dudasdavid/MaM2019/Mechanics/STL/mainframe/pcb_holder.STL

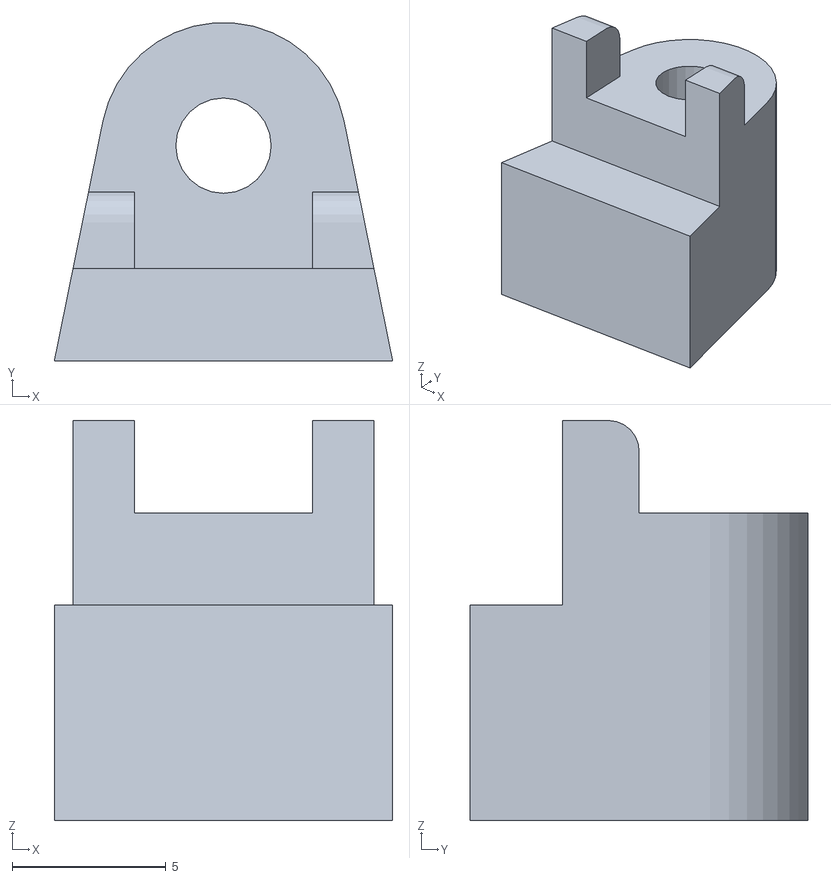
[picture p17: CAD file, 2020-09-13]
Mechanics/STL/mainframe/pcb_holder.STL
11.0 x 11.0 x 13.0
