dudasdavid/MaM2019/Mechanics/STL/tower/rib.STL

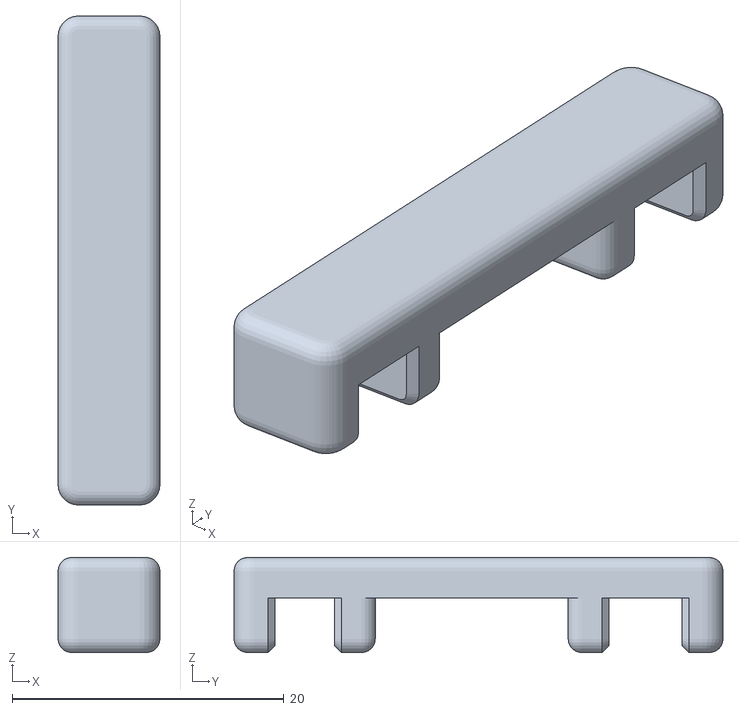
[picture p18: CAD file, 2020-09-15]
Mechanics/STL/tower/rib.STL
7.50 x 36.0 x 7.00
