dudasdavid/MaM2019/Mechanics/Gear design/spur_gear.dxf

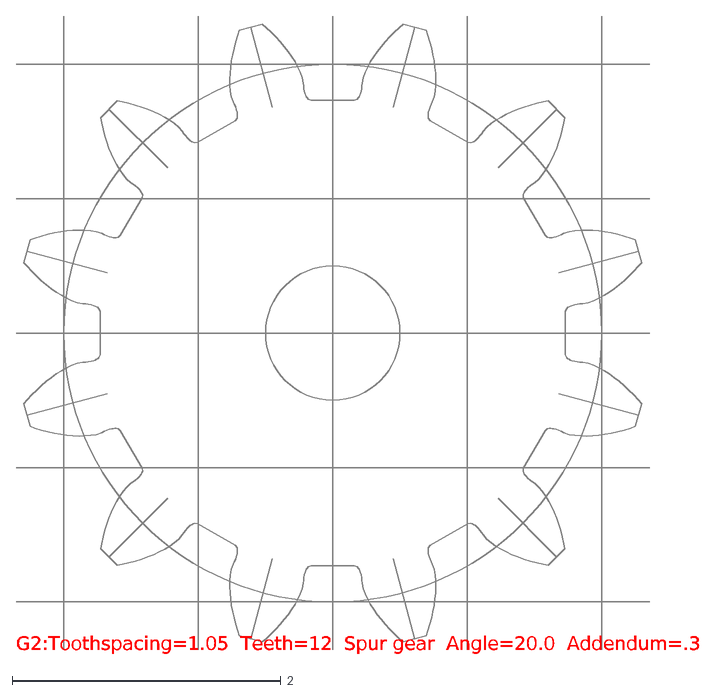
[picture p19: CAD file, 2019-07-08]
Mechanics/Gear design/spur_gear.dxf
G2:Toothspacing=1.05 Teeth=12 Spur gear Angle=20.0 Addendum=.3
