dudasdavid/MaM2019/Mechanics/Solidworks/SG90/microservoArm.SLDPRT

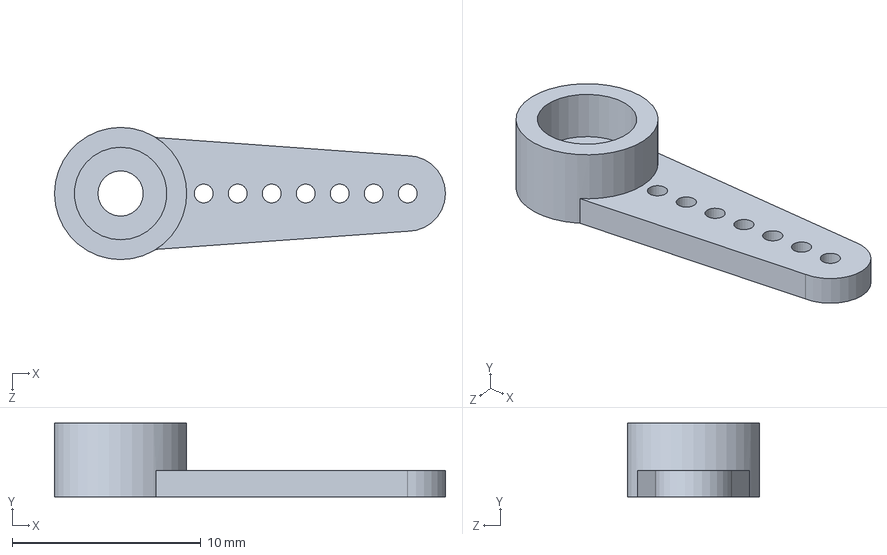
[picture p20: CAD file, 2020-09-13]
Mechanics/Solidworks/SG90/microservoArm.SLDPRT
20.7 x 3.90 x 7.00 mm
