dudasdavid/MaM2019/Mechanics/STL/camera/part1.STL

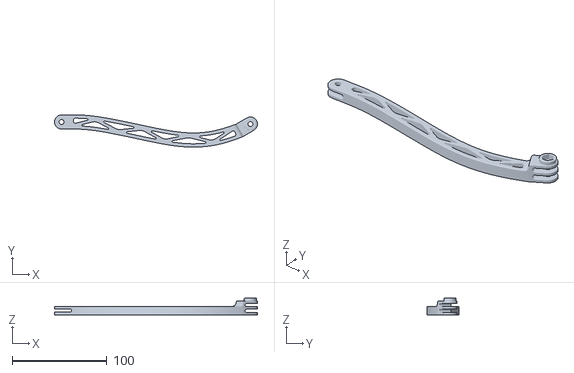
[picture p21: CAD file, 2020-09-19]
Mechanics/STL/camera/part1.STL
214.4 x 34.1 x 17.8
