dudasdavid/MaM2019/Mechanics/STL/ejector/cap.STL

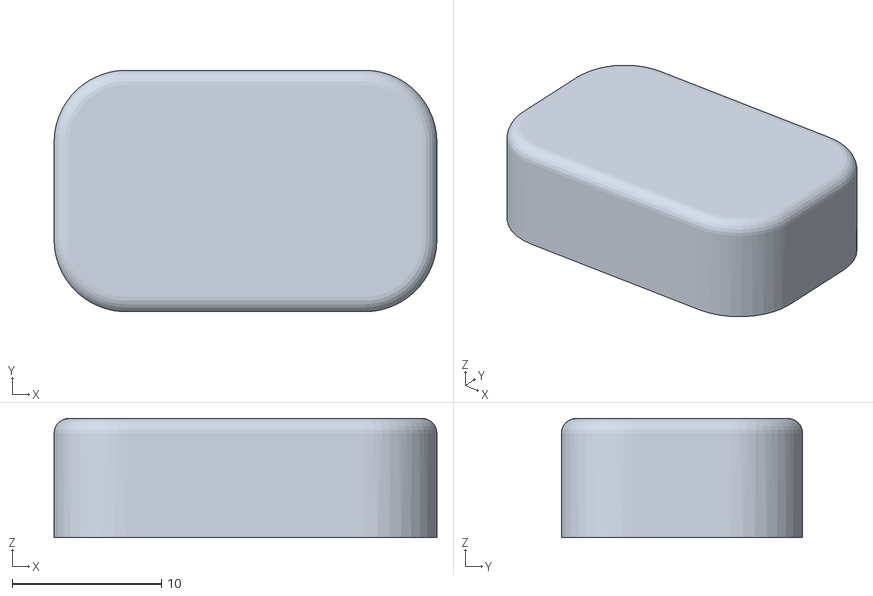
[picture p22: CAD file, 2020-09-15]
Mechanics/STL/ejector/cap.STL
25.7 x 16.2 x 8.00
