dudasdavid/MaM2019/Mechanics/STL/mainframe/side2_unmirrored.STL

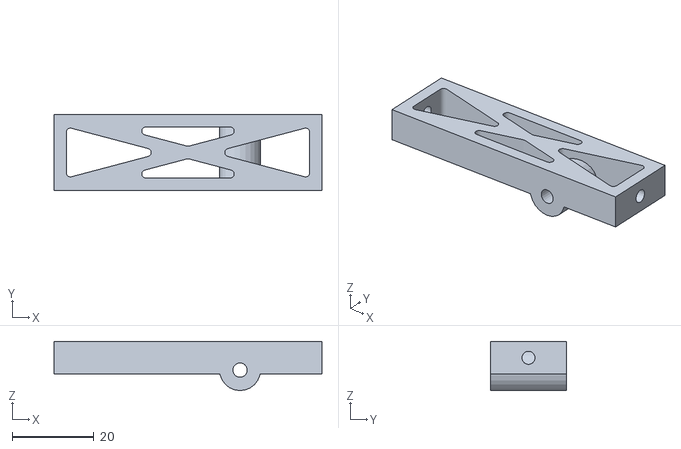
[picture p23: CAD file, 2020-09-13]
Mechanics/STL/mainframe/side2_unmirrored.STL
65.4 x 18.5 x 12.0
