dudasdavid/MaM2019/Mechanics/STL/tower/COLLECTOR2.STL

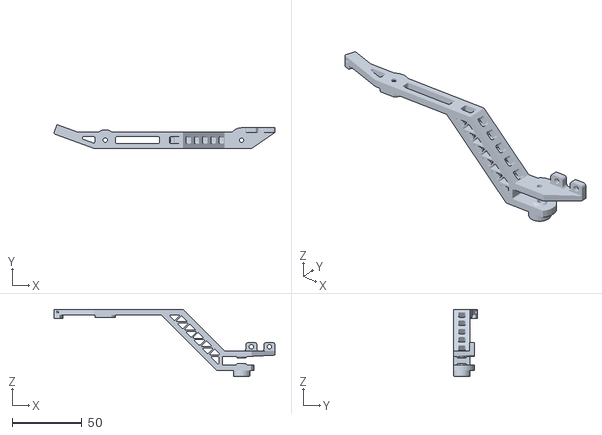
[picture p24: CAD file, 2020-09-13]
Mechanics/STL/tower/COLLECTOR2.STL
158.8 x 17.2 x 48.5
