dudasdavid/MaM2019/Mechanics/Gear design/gears_v1.dxf

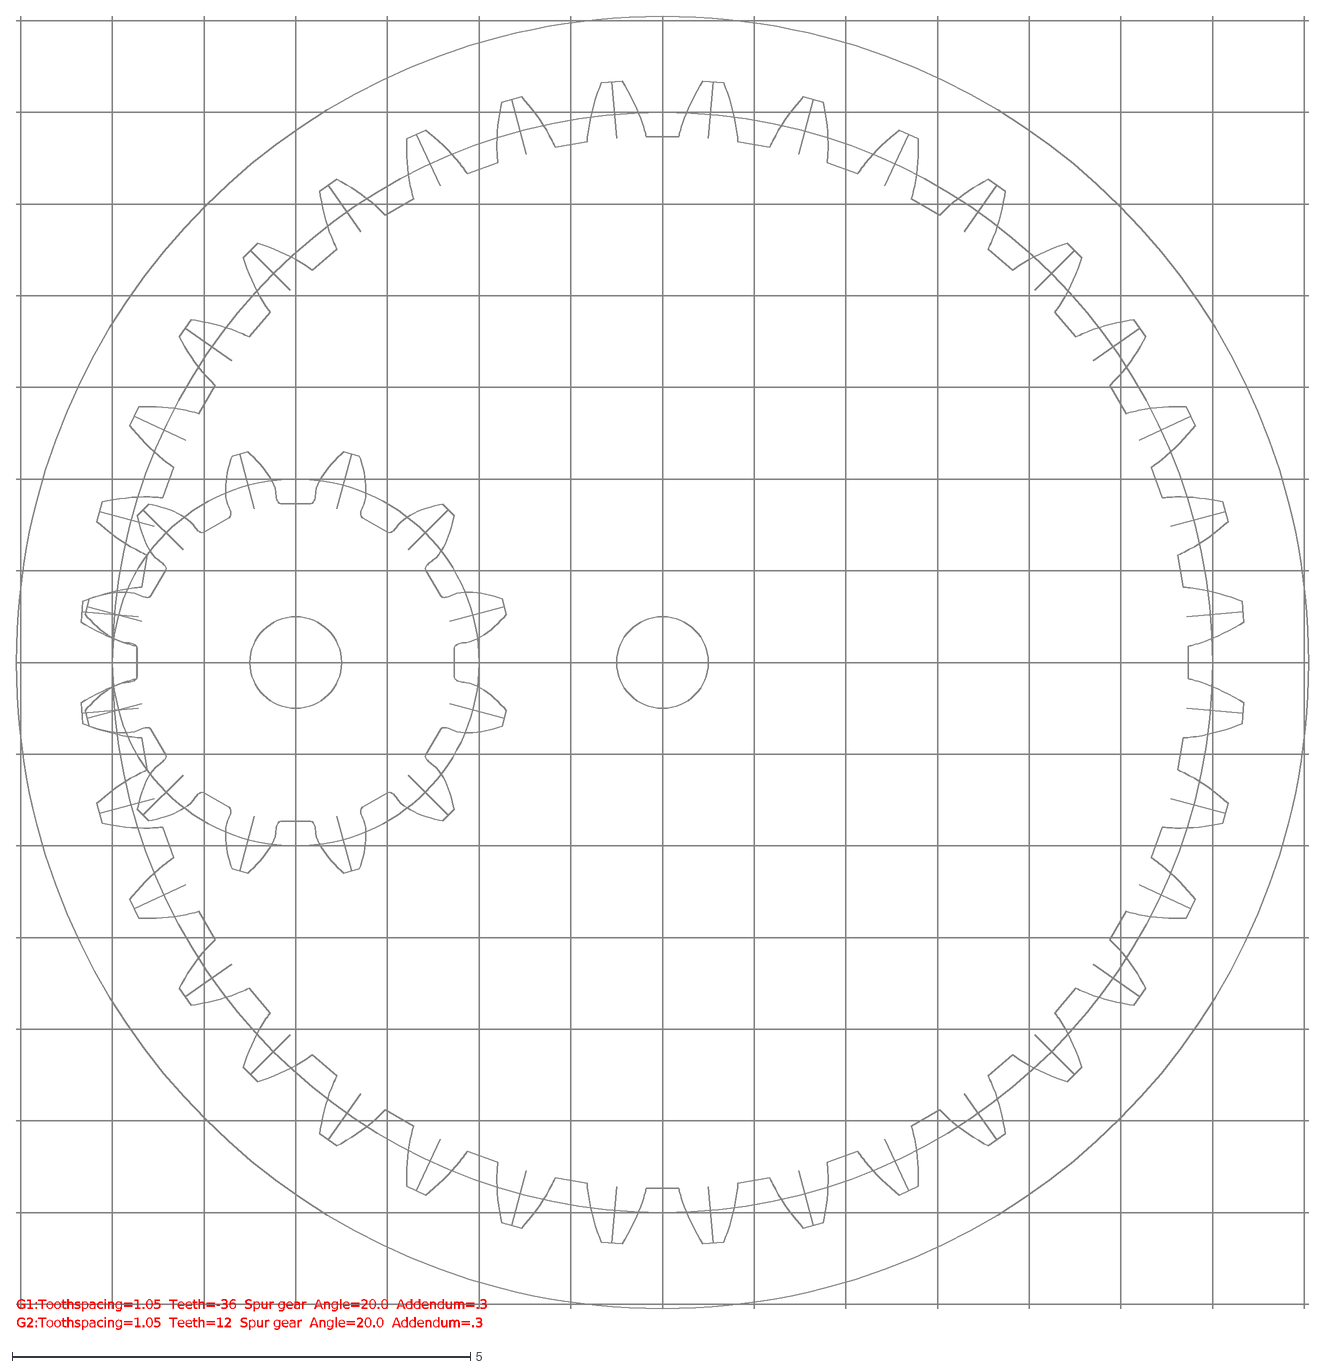
[picture p25: CAD file, 2019-07-08]
Mechanics/Gear design/gears_v1.dxf
G1:Toothspacing=1.05 Teeth=-36 Spur gear Angle=20.0 Addendum=.3
G2:Toothspacing=1.05 Teeth=12 Spur gear Angle=20.0 Addendum=.3
