dudasdavid/MaM2019/Mechanics/STL/camera/camera_frame.STL

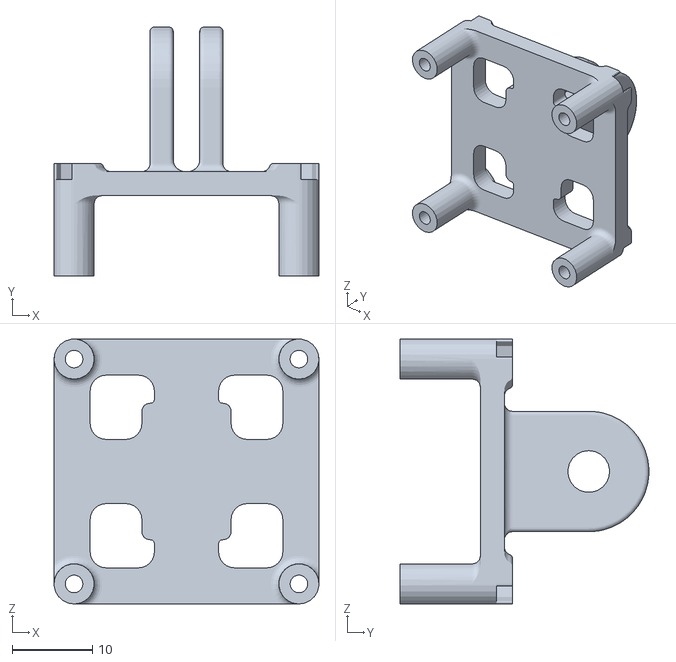
[picture p26: CAD file, 2020-09-19]
Mechanics/STL/camera/camera_frame.STL
33.0 x 31.0 x 33.0
