dudasdavid/MaM2019/Mechanics/STL/ejector/arm.STL

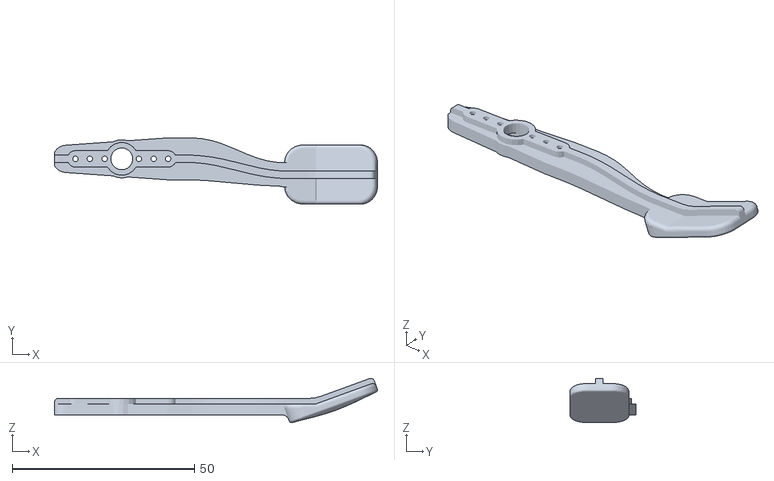
[picture p27: CAD file, 2020-09-15]
Mechanics/STL/ejector/arm.STL
88.5 x 18.2 x 12.2
