dudasdavid/MaM2019/Mechanics/STL/mainframe/base_1.STL

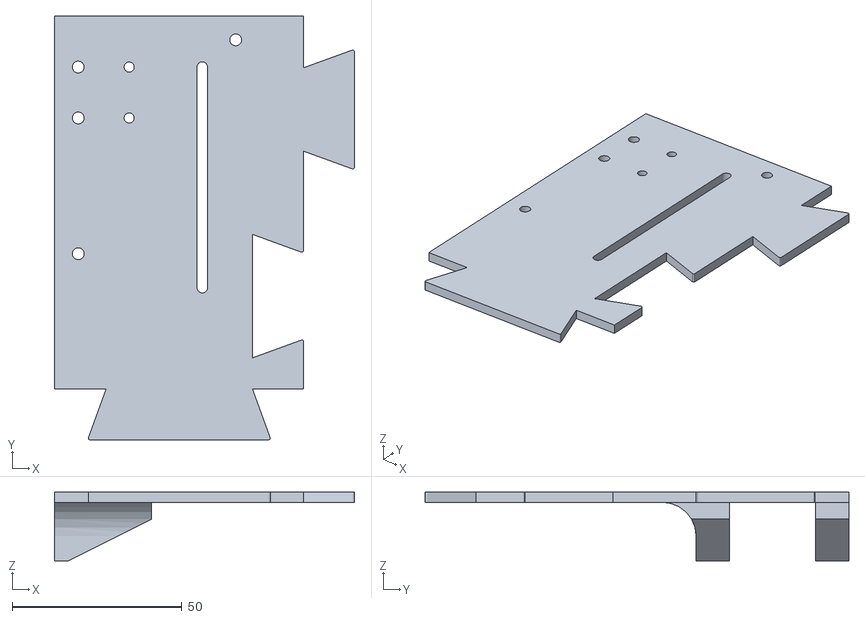
[picture p28: CAD file, 2020-09-13]
Mechanics/STL/mainframe/base_1.STL
88.4 x 124.8 x 20.3
