dudasdavid/MaM2019/Mechanics/STL/tower/COLLECTOR3.STL

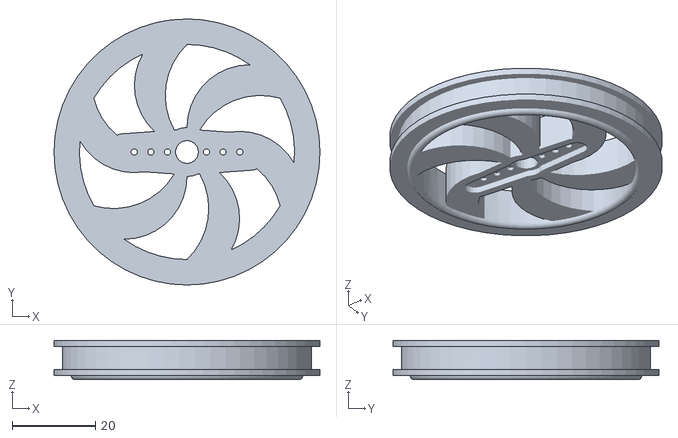
[picture p29: CAD file, 2020-09-13]
Mechanics/STL/tower/COLLECTOR3.STL
64.0 x 64.0 x 9.50
