dudasdavid/MaM2019/Mechanics/STL/camera/part2.STL

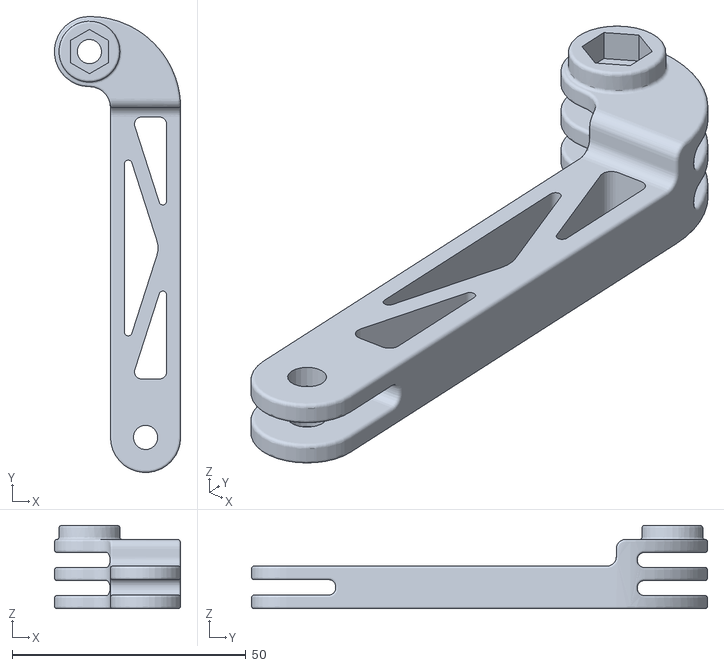
[picture p30: CAD file, 2020-09-19]
Mechanics/STL/camera/part2.STL
27.0 x 97.5 x 17.8
