dudasdavid/MaM2019/Mechanics/STL/ejector/bag.STL

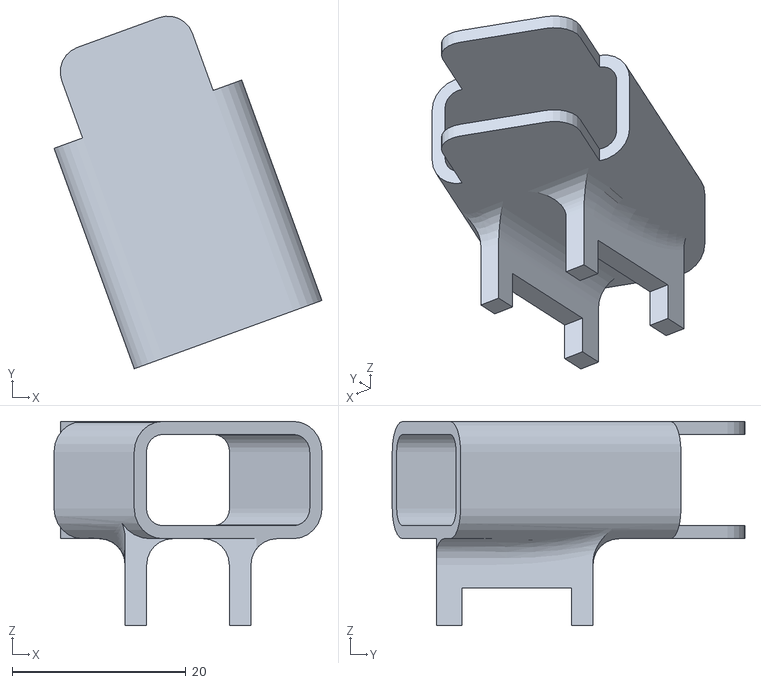
[picture p31: CAD file, 2020-09-15]
Mechanics/STL/ejector/bag.STL
30.8 x 40.6 x 23.5
