dudasdavid/MaM2019/Mechanics/STL/mainframe/side1_unmirrored.STL

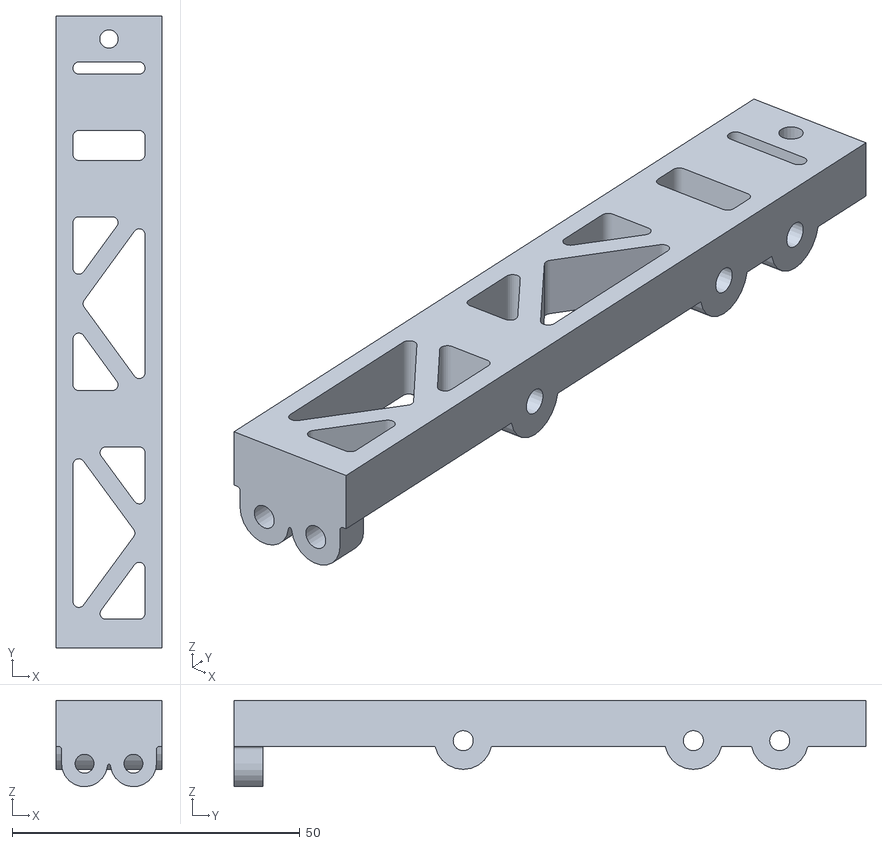
[picture p32: CAD file, 2020-09-13]
Mechanics/STL/mainframe/side1_unmirrored.STL
18.5 x 109.8 x 15.0
