dudasdavid/MaM2019/Mechanics/STL/tower/right.STL

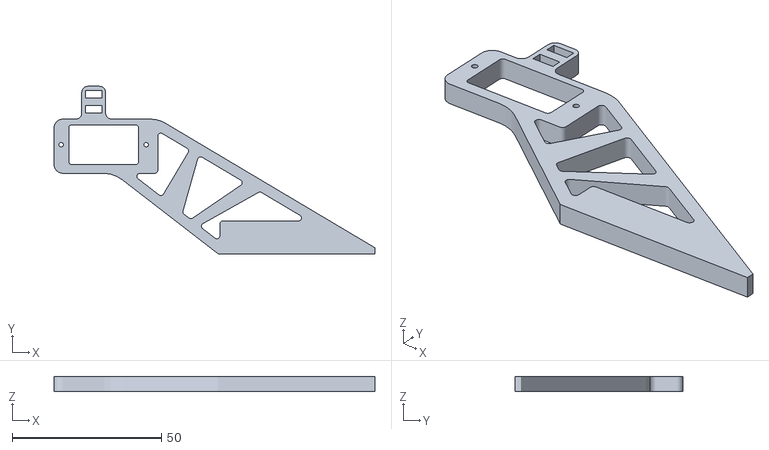
[picture p33: CAD file, 2020-09-13]
Mechanics/STL/tower/right.STL
107.6 x 56.1 x 5.00
