dudasdavid/MaM2019/Mechanics/STL/ejector/ball_remover.STL

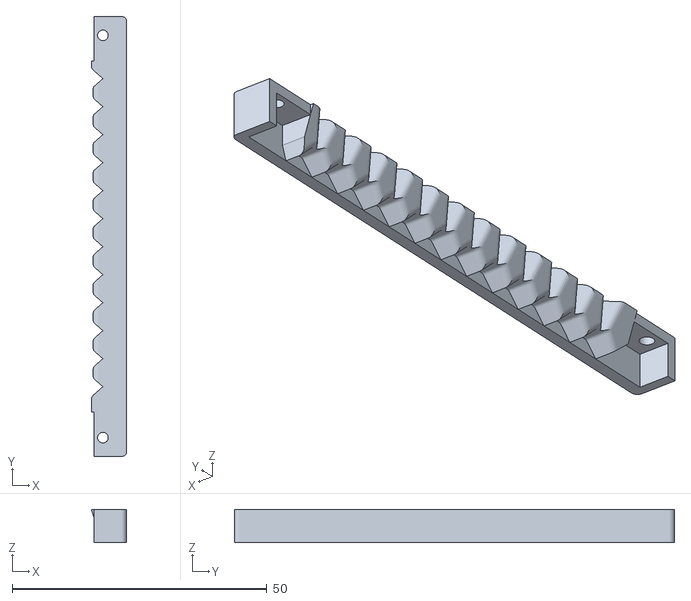
[picture p34: CAD file, 2020-09-15]
Mechanics/STL/ejector/ball_remover.STL
6.97 x 86.4 x 6.50
