dudasdavid/MaM2019/Mechanics/STL/mainframe/base_2.STL

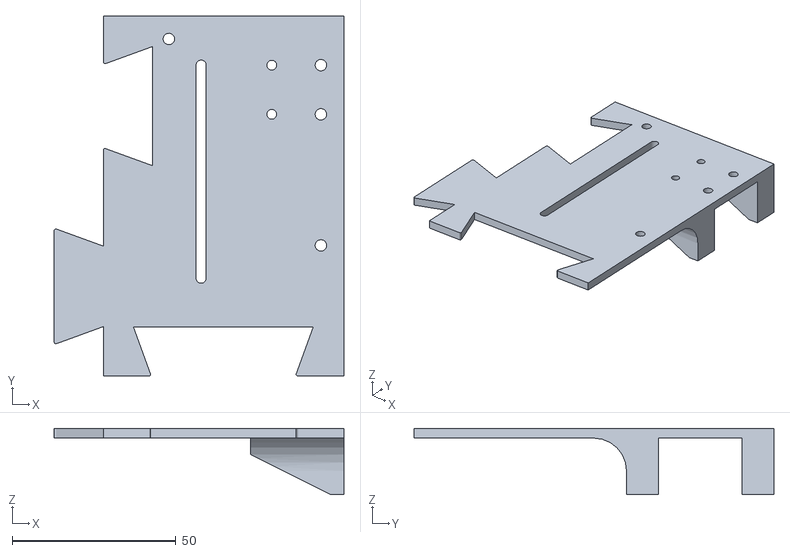
[picture p35: CAD file, 2020-09-13]
Mechanics/STL/mainframe/base_2.STL
88.4 x 109.8 x 20.3
