dudasdavid/MaM2019/Mechanics/STL/tower/COLLECTOR6.STL

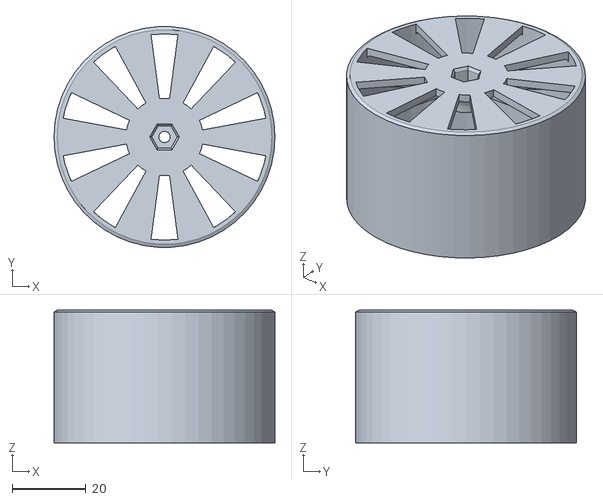
[picture p36: CAD file, 2020-09-13]
Mechanics/STL/tower/COLLECTOR6.STL
60.0 x 59.9 x 36.0
