dudasdavid/MaM2019/Mechanics/STL/tower/balance2.STL

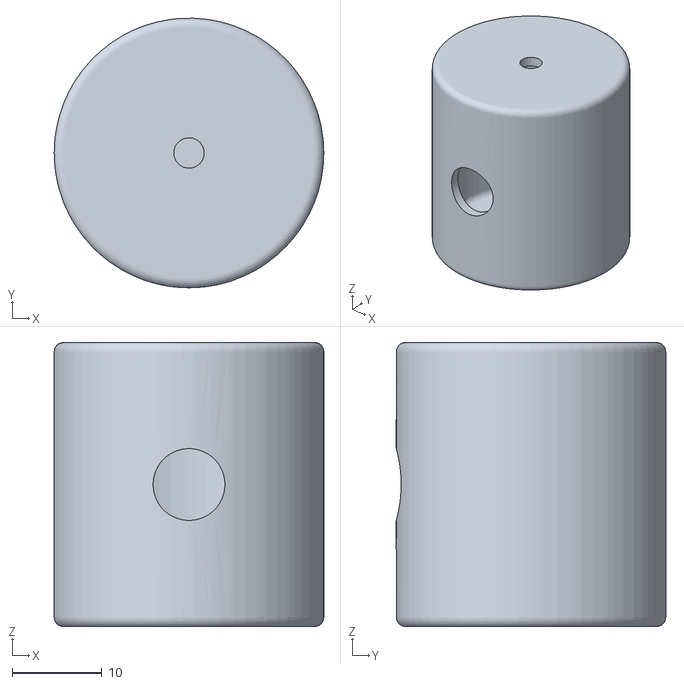
[picture p37: CAD file, 2020-09-13]
Mechanics/STL/tower/balance2.STL
30.0 x 30.0 x 31.6
