dudasdavid/MaM2019/Mechanics/STL/tower/balance1.STL

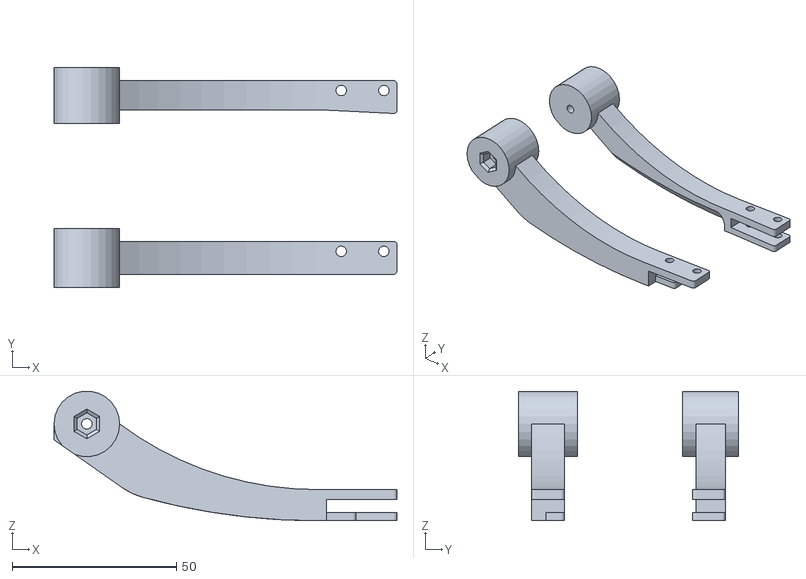
[picture p38: CAD file, 2020-09-13]
Mechanics/STL/tower/balance1.STL
104.5 x 67.0 x 39.4
