dudasdavid/MaM2019/Mechanics/STL/tower/COLLECTOR4.STL

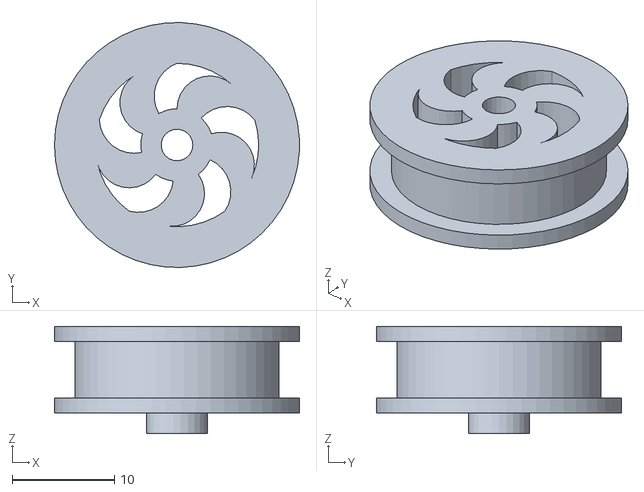
[picture p39: CAD file, 2020-09-13]
Mechanics/STL/tower/COLLECTOR4.STL
24.0 x 24.0 x 10.5
