dudasdavid/MaM2019/Mechanics/Solidworks/RingGear_corrected_diameter.SLDPRT

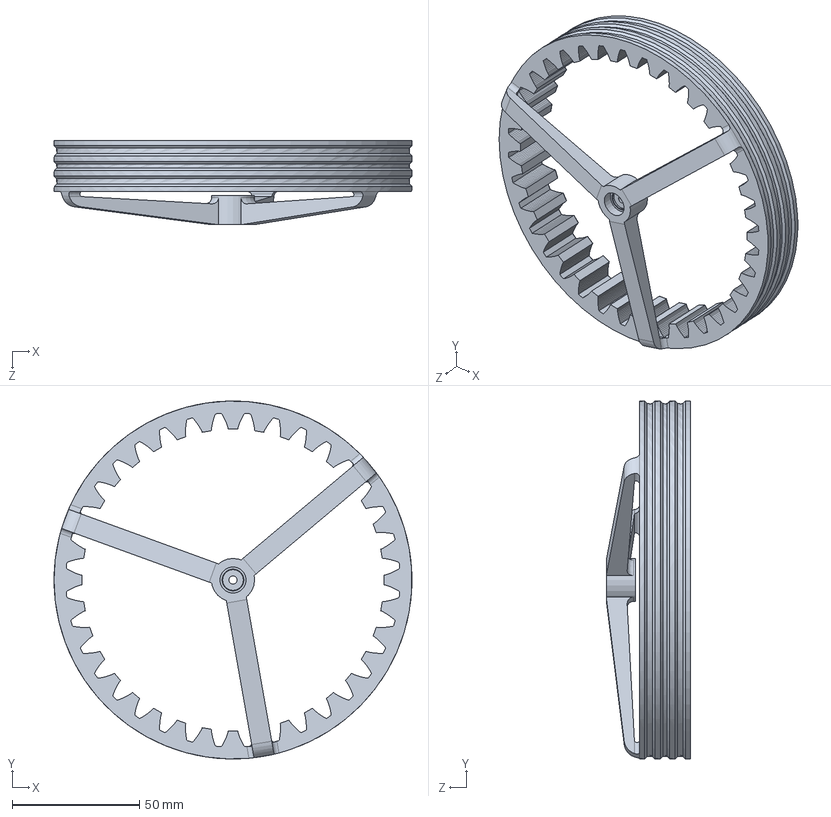
[picture p40: CAD file, 2020-09-13]
Mechanics/Solidworks/RingGear_corrected_diameter.SLDPRT
140.9 x 140.9 x 33.0 mm
