dudasdavid/MaM2019/Mechanics/STL/tower/middle.STL

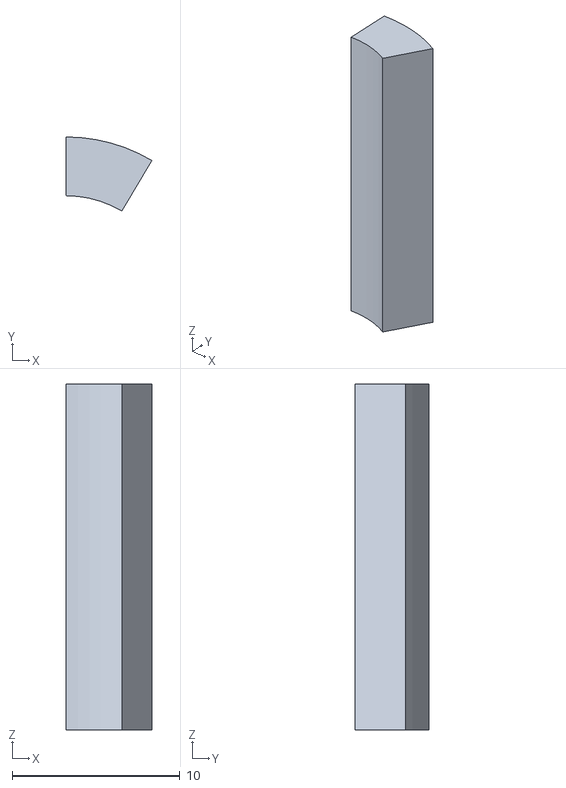
[picture p41: CAD file, 2020-09-13]
Mechanics/STL/tower/middle.STL
5.11 x 4.41 x 20.6
