dudasdavid/MaM2019/Mechanics/Solidworks/RubberTire shrinked.SLDPRT

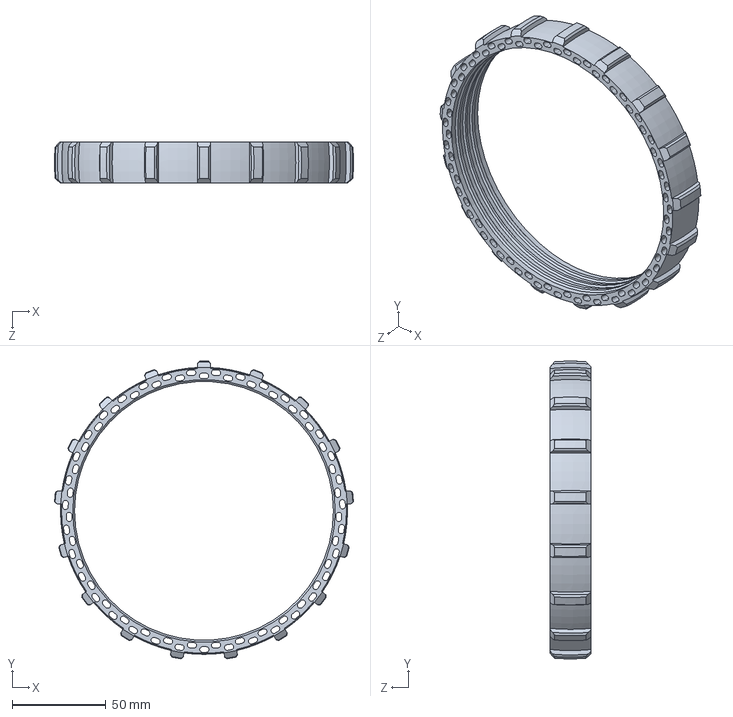
[picture p42: CAD file, 2020-09-13]
Mechanics/Solidworks/RubberTire shrinked.SLDPRT
159.1 x 158.5 x 22.0 mm
