dudasdavid/MaM2019/Mechanics/STL/tower/COLLECTOR1.STL

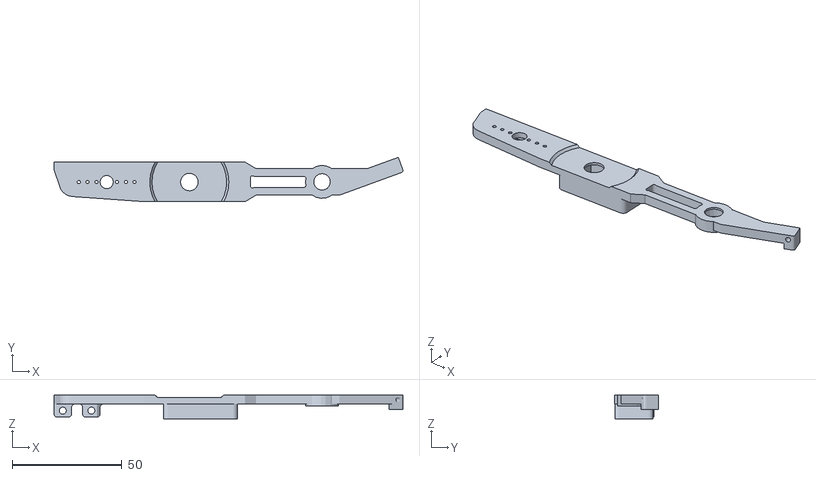
[picture p43: CAD file, 2020-09-13]
Mechanics/STL/tower/COLLECTOR1.STL
158.8 x 20.2 x 10.7
