dudasdavid/MaM2019/Mechanics/Solidworks/RingGear.SLDPRT

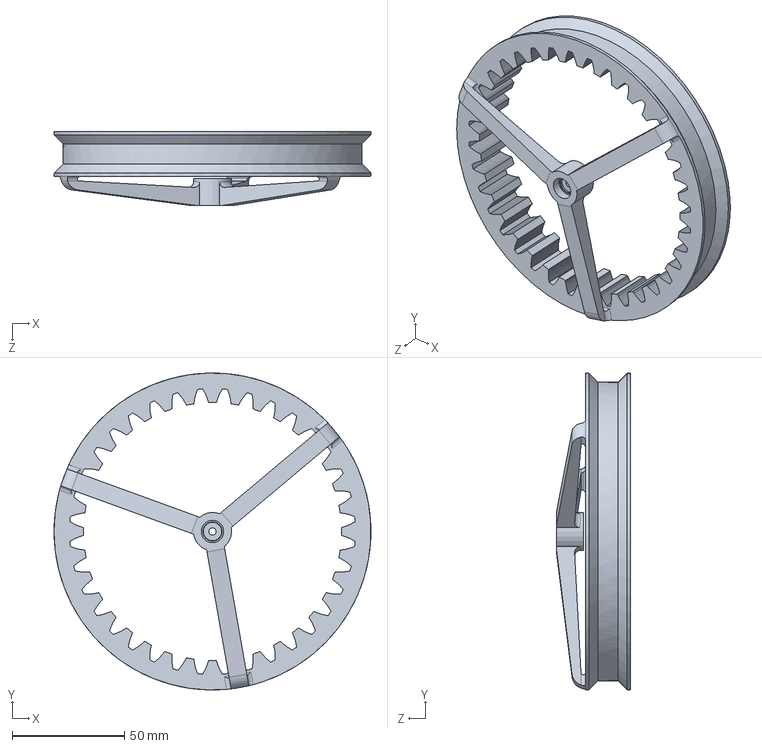
[picture p44: CAD file, 2020-09-13]
Mechanics/Solidworks/RingGear.SLDPRT
140.9 x 140.9 x 33.0 mm
