dudasdavid/MaM2019/Mechanics/STL/tower/base.STL

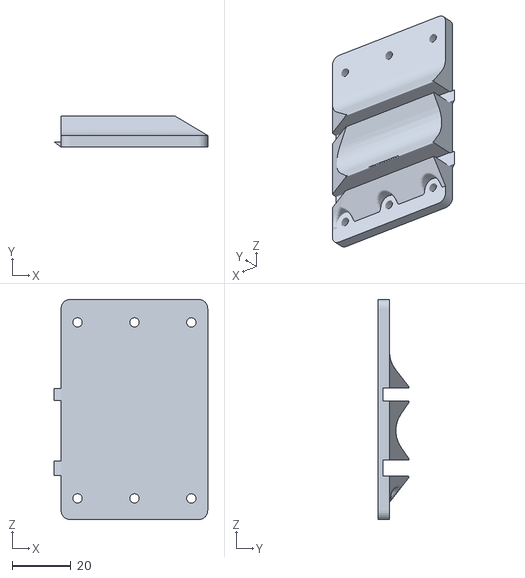
[picture p45: CAD file, 2020-09-13]
Mechanics/STL/tower/base.STL
52.3 x 10.7 x 75.0
