dudasdavid/MaM2019/Mechanics/Solidworks/Lbracket.sldprt

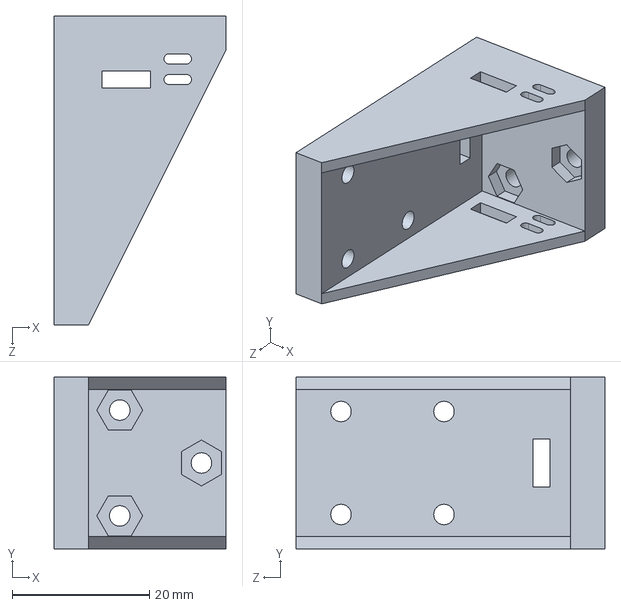
[picture p46: CAD file, 2020-09-13]
Mechanics/Solidworks/Lbracket.sldprt
25.0 x 25.0 x 45.0 mm
