dudasdavid/MaM2019/Mechanics/STL/tower/COLLECTOR5.STL

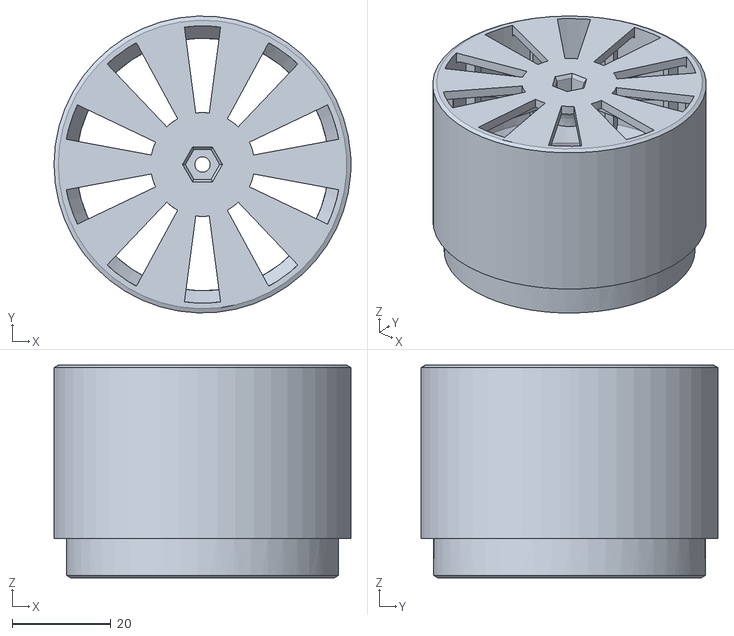
[picture p47: CAD file, 2020-09-13]
Mechanics/STL/tower/COLLECTOR5.STL
60.0 x 60.0 x 43.0
