dudasdavid/MaM2019/Mechanics/Solidworks/BasePlate.sldprt

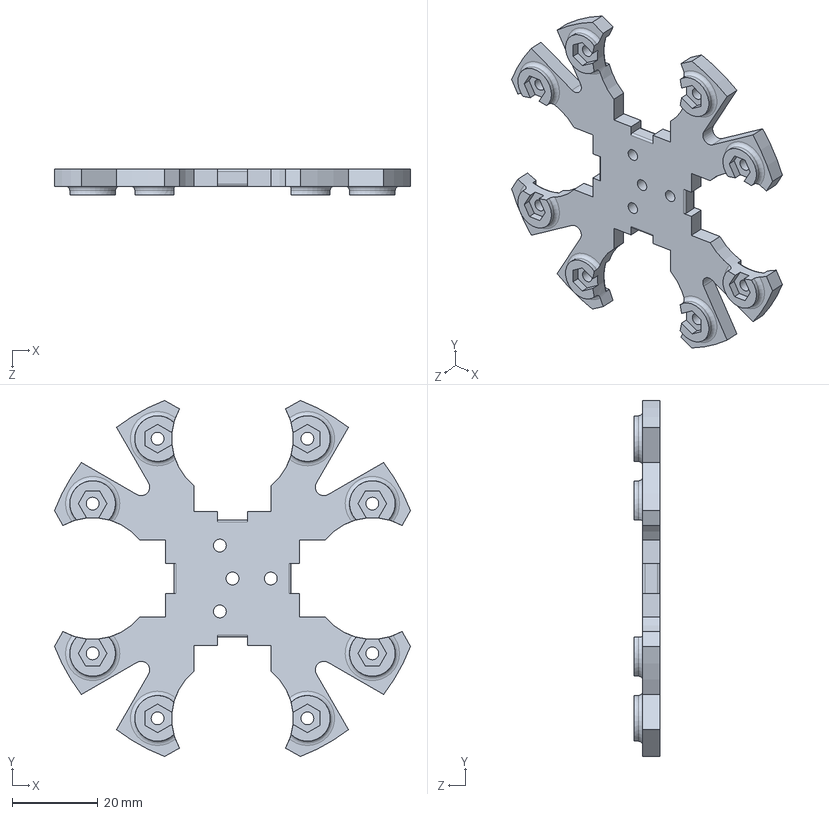
[picture p48: CAD file, 2020-09-13]
Mechanics/Solidworks/BasePlate.sldprt
83.2 x 83.2 x 6.00 mm
