dudasdavid/MaM2019/Mechanics/STL/tower/left.STL

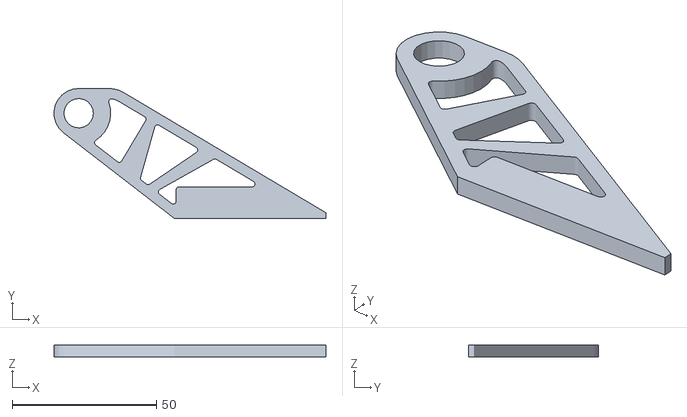
[picture p49: CAD file, 2020-09-13]
Mechanics/STL/tower/left.STL
94.4 x 45.1 x 4.00
