dudasdavid/MaM2019/Mechanics/Solidworks/SpurRibs_corrected.sldprt

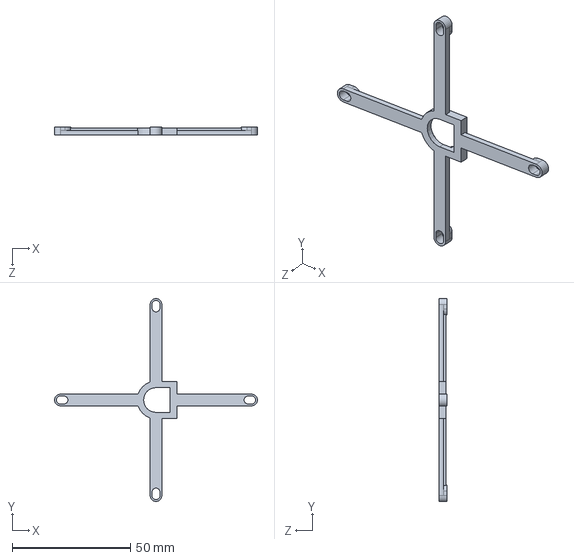
[picture p50: CAD file, 2020-09-13]
Mechanics/Solidworks/SpurRibs_corrected.sldprt
86.0 x 86.0 x 3.50 mm
