dudasdavid/MaM2019/Mechanics/Solidworks/SpurGear.SLDPRT

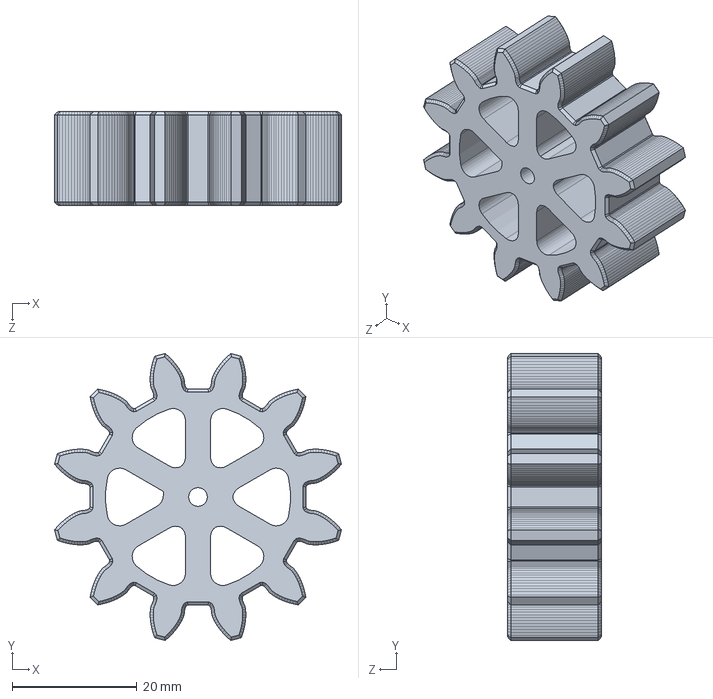
[picture p51: CAD file, 2020-09-13]
Mechanics/Solidworks/SpurGear.SLDPRT
45.9 x 45.9 x 15.0 mm
