dudasdavid/MaM2019/Mechanics/Solidworks/El2 - 28BYJ-48 - 5 VDC.SLDPRT

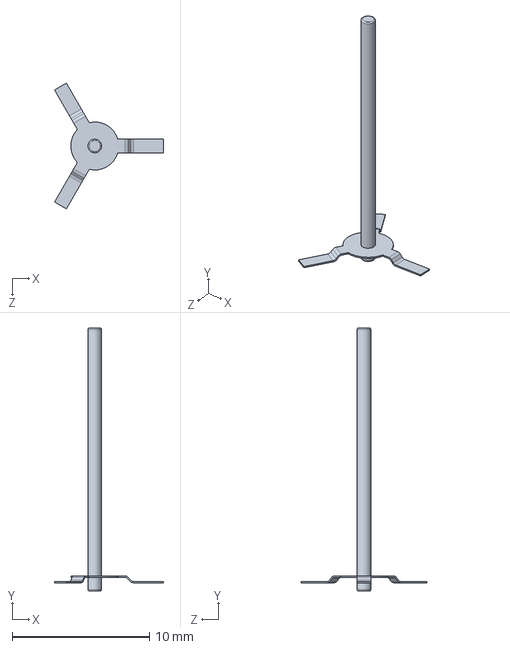
[picture p52: CAD file, 2020-09-13]
Mechanics/Solidworks/El2 - 28BYJ-48 - 5 VDC.SLDPRT
7.93 x 19.1 x 9.16 mm
