dudasdavid/MaM2019/Mechanics/Solidworks/El7 - 28BYJ-48 - 5 VDC.SLDPRT

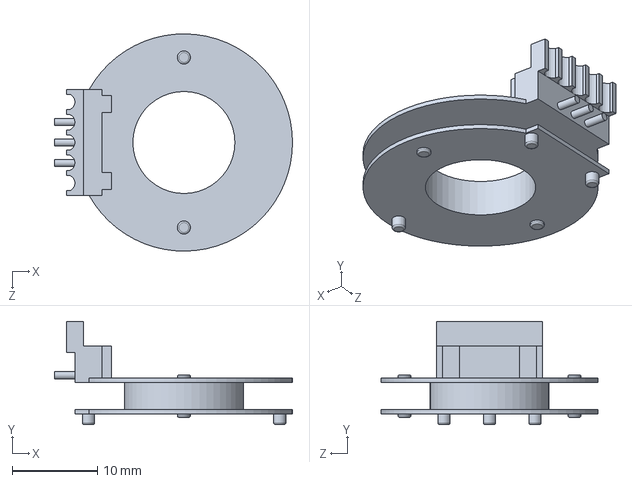
[picture p53: CAD file, 2020-09-13]
Mechanics/Solidworks/El7 - 28BYJ-48 - 5 VDC.SLDPRT
28.0 x 12.1 x 25.5 mm
