dudasdavid/MaM2019/Mechanics/Solidworks/El8 - 28BYJ-48 - 5 VDC.SLDPRT

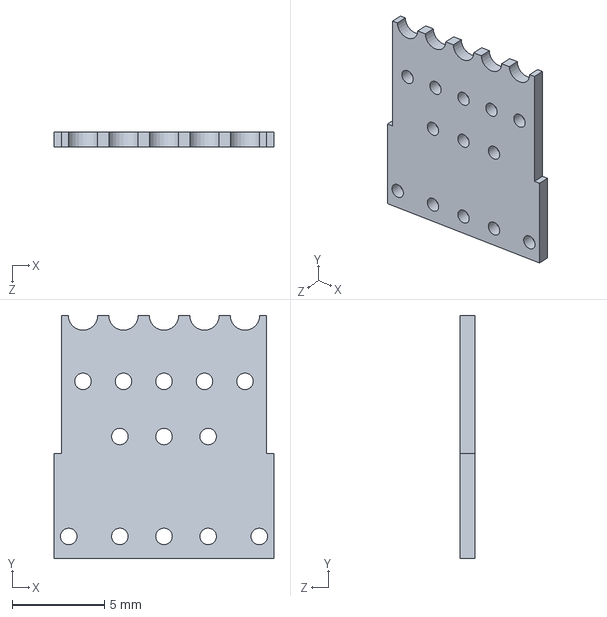
[picture p54: CAD file, 2020-09-13]
Mechanics/Solidworks/El8 - 28BYJ-48 - 5 VDC.SLDPRT
11.9 x 13.2 x 0.8 mm
