dudasdavid/MaM2019/Mechanics/Solidworks/El14 - 28BYJ-48 - 5 VDC.SLDPRT

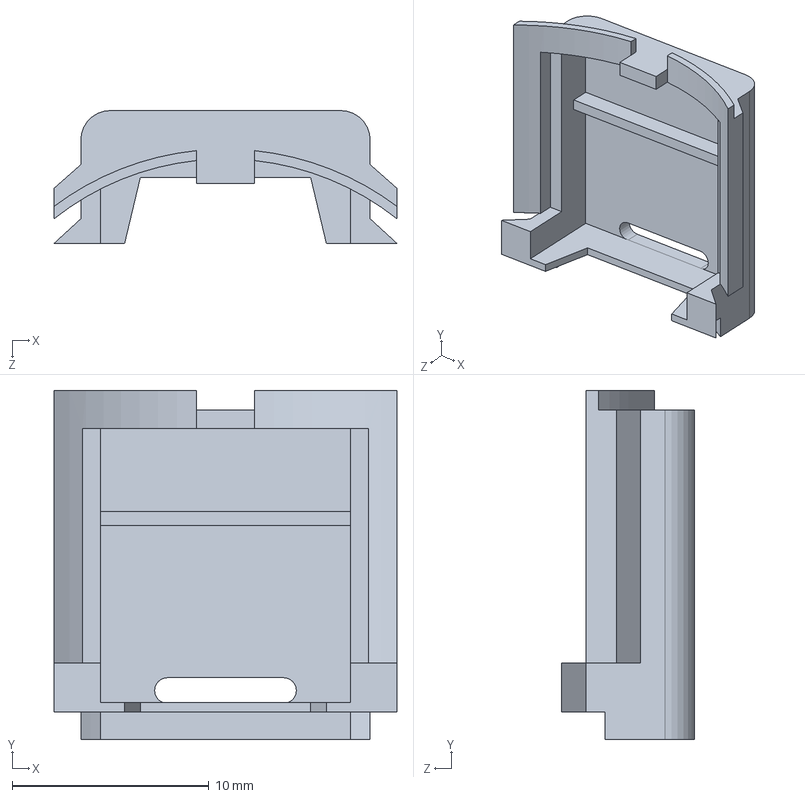
[picture p55: CAD file, 2020-09-13]
Mechanics/Solidworks/El14 - 28BYJ-48 - 5 VDC.SLDPRT
17.4 x 17.8 x 6.75 mm
