dudasdavid/MaM2019/Mechanics/Solidworks/El11 - 28BYJ-48 - 5 VDC.SLDPRT

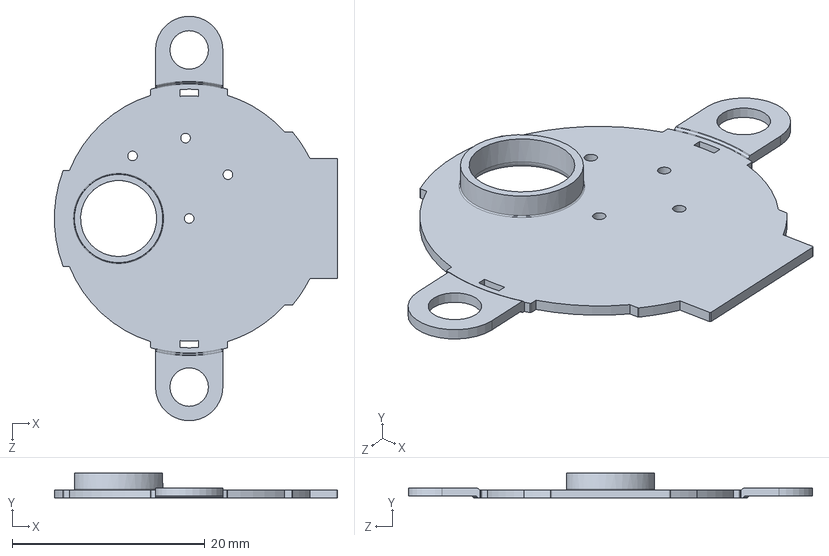
[picture p56: CAD file, 2020-09-13]
Mechanics/Solidworks/El11 - 28BYJ-48 - 5 VDC.SLDPRT
29.4 x 2.57 x 42.0 mm
