dudasdavid/MaM2019/Mechanics/Solidworks/El4 - 28BYJ-48 - 5 VDC.SLDPRT

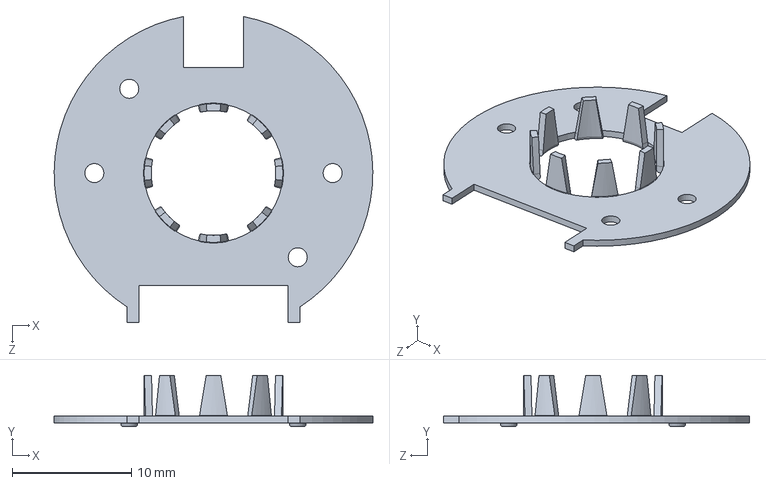
[picture p57: CAD file, 2020-09-13]
Mechanics/Solidworks/El4 - 28BYJ-48 - 5 VDC.SLDPRT
26.7 x 4.30 x 25.7 mm
