dudasdavid/MaM2019/Mechanics/Solidworks/El9 - 28BYJ-48 - 5 VDC.SLDPRT

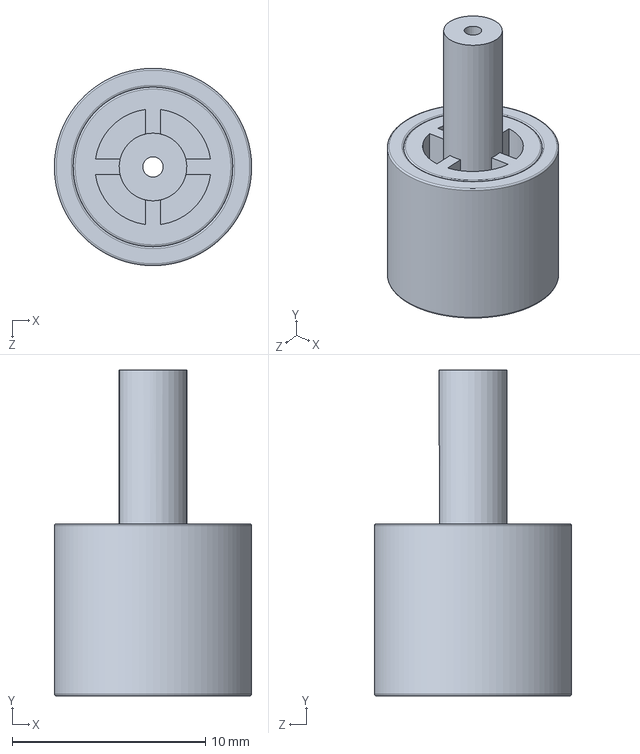
[picture p58: CAD file, 2020-09-13]
Mechanics/Solidworks/El9 - 28BYJ-48 - 5 VDC.SLDPRT
10.2 x 16.9 x 10.2 mm
