dudasdavid/MaM2019/Mechanics/Solidworks/El12 - 28BYJ-48 - 5 VDC.SLDPRT

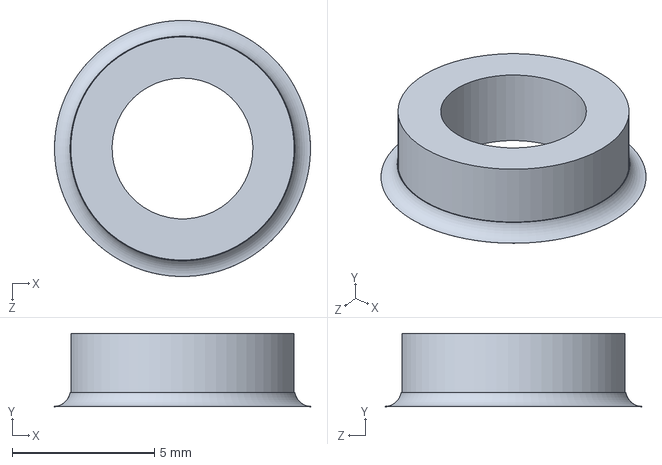
[picture p59: CAD file, 2020-09-13]
Mechanics/Solidworks/El12 - 28BYJ-48 - 5 VDC.SLDPRT
9.00 x 2.57 x 9.00 mm
