dudasdavid/MaM2019/Mechanics/Solidworks/El6 - 28BYJ-48 - 5 VDC.SLDPRT

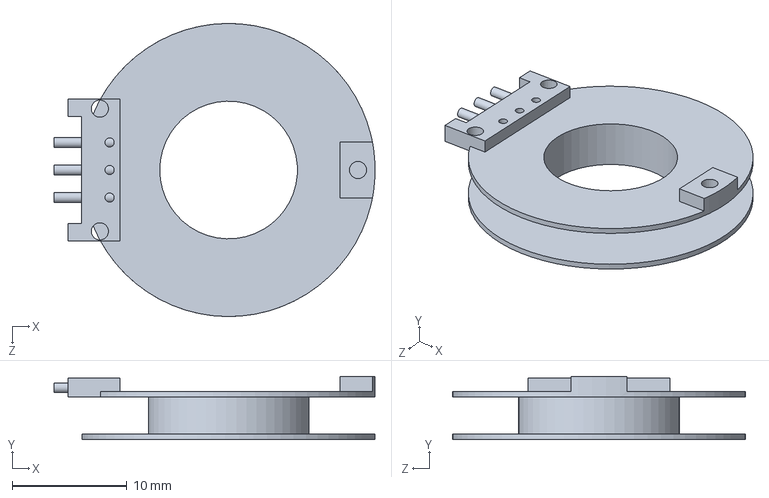
[picture p60: CAD file, 2020-09-13]
Mechanics/Solidworks/El6 - 28BYJ-48 - 5 VDC.SLDPRT
28.0 x 5.50 x 25.5 mm
