dudasdavid/MaM2019/Mechanics/Solidworks/El10 - 28BYJ-48 - 5 VDC.SLDPRT

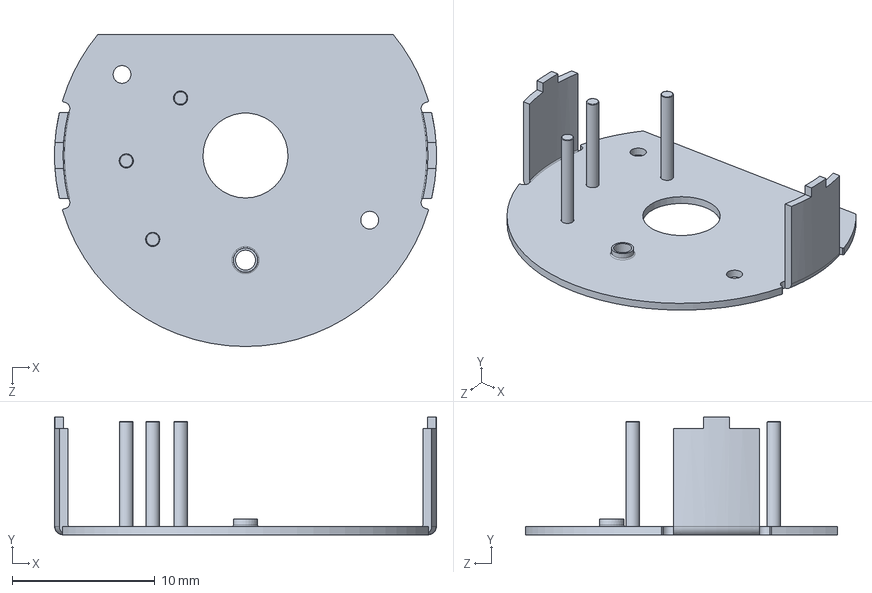
[picture p61: CAD file, 2020-09-13]
Mechanics/Solidworks/El10 - 28BYJ-48 - 5 VDC.SLDPRT
26.8 x 8.25 x 21.9 mm
