dudasdavid/MaM2019/Mechanics/Solidworks/El13 - 28BYJ-48 - 5 VDC.SLDPRT

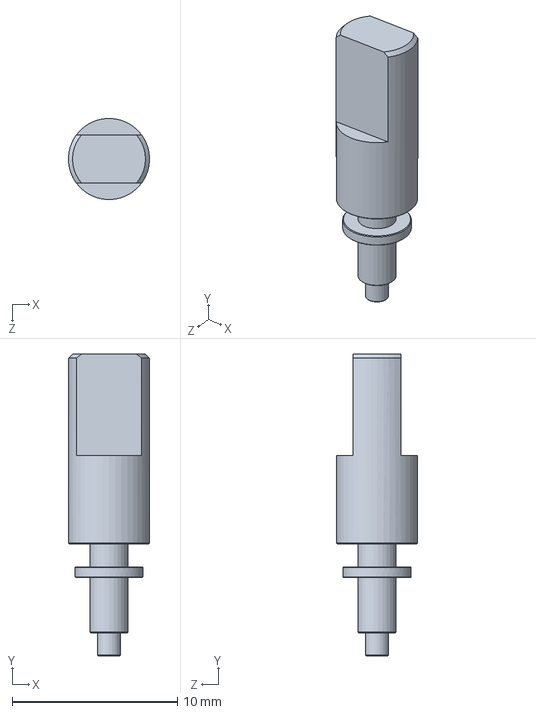
[picture p62: CAD file, 2020-09-13]
Mechanics/Solidworks/El13 - 28BYJ-48 - 5 VDC.SLDPRT
4.92 x 18.3 x 4.92 mm
