dudasdavid/MaM2019/Mechanics/Solidworks/El1 - 28BYJ-48 - 5 VDC.SLDPRT

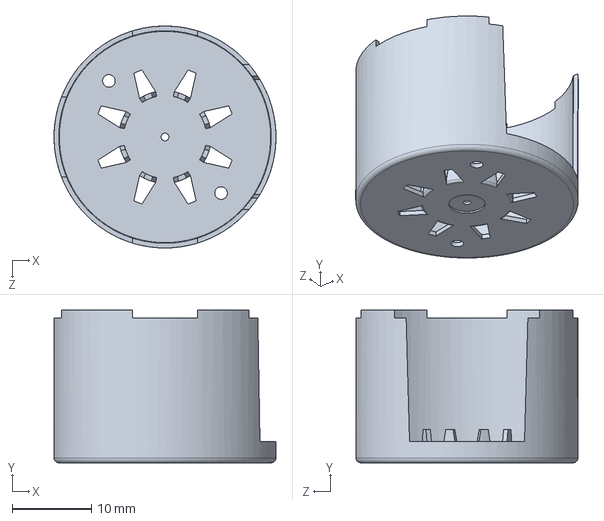
[picture p63: CAD file, 2020-09-13]
Mechanics/Solidworks/El1 - 28BYJ-48 - 5 VDC.SLDPRT
28.0 x 19.2 x 28.0 mm
